Lmart89/MikroPrintr-3D/3D RENDERS/MK2560EM-G v1G-6.png

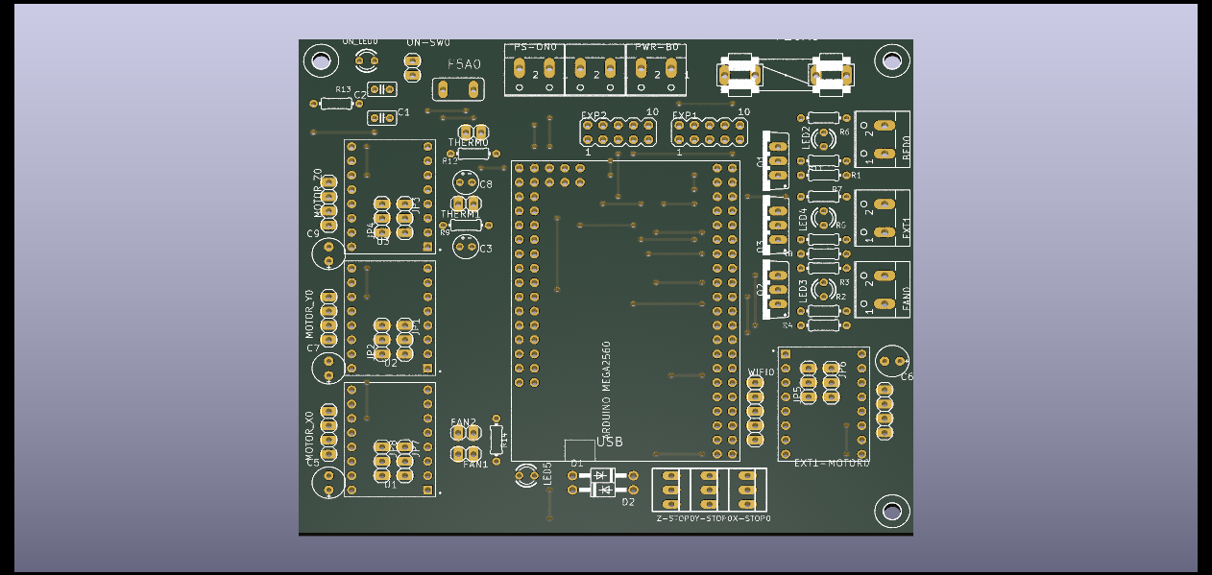
3D RENDERS/MK2560EM-G v1G-6.png
