Lmart89/MikroPrintr-3D/3D RENDERS/MK2560EM-G v1G-FLAT_PCB_SIZES.png

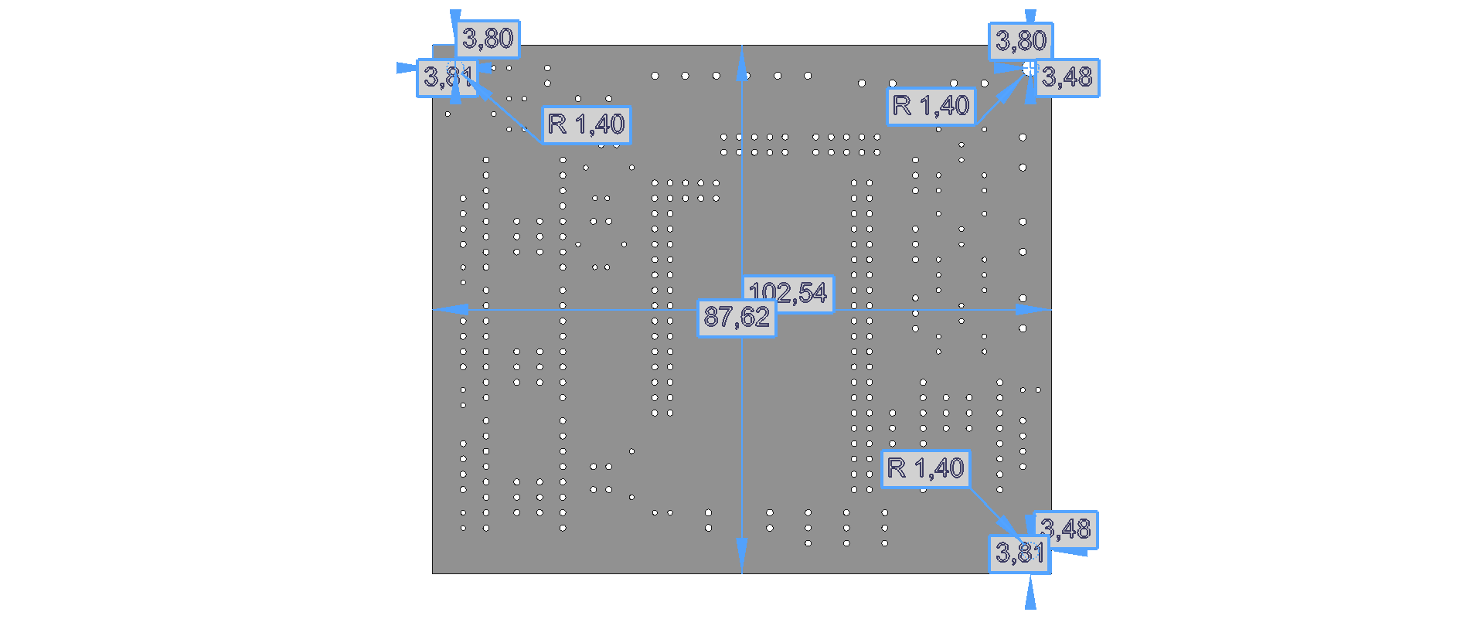
3D RENDERS/MK2560EM-G v1G-FLAT_PCB_SIZES.png
