Lmart89/MikroPrintr-3D/DIAGRAMAS/MK2560EMG-V2/mk2560G-v2.png

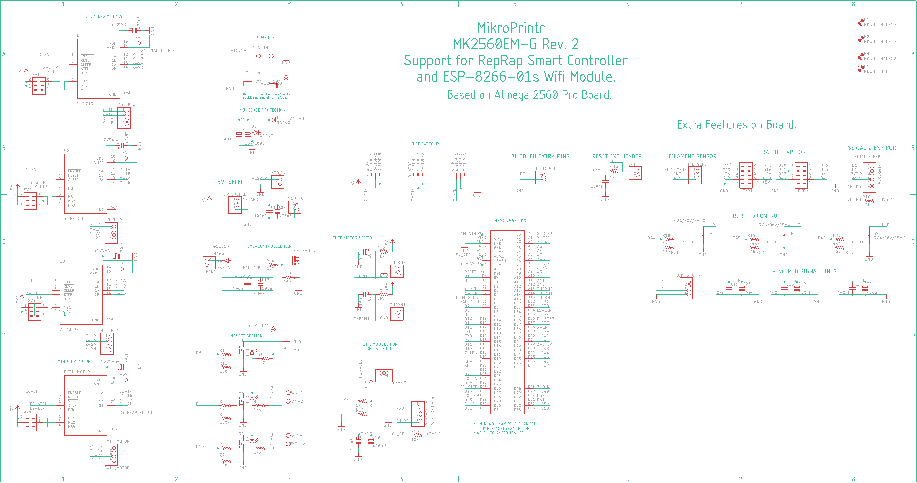
DIAGRAMAS/MK2560EMG-V2/mk2560G-v2.png
