Lmart89/MikroPrintr-3D/Printable Parts/Skylab Variant/medidas_skylab/Extrusor_12 dimensiones 3.png

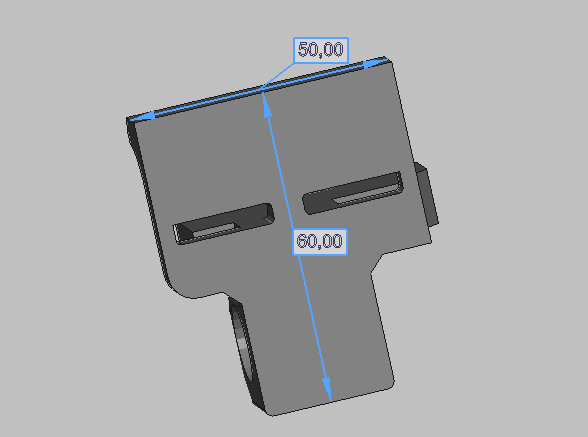
Printable Parts/Skylab Variant/medidas_skylab/Extrusor_12 dimensiones 3.png
