Lmart89/MikroPrintr-3D/Printable Parts/Skylab Variant/medidas_skylab/Z1 dimensiones 2.png

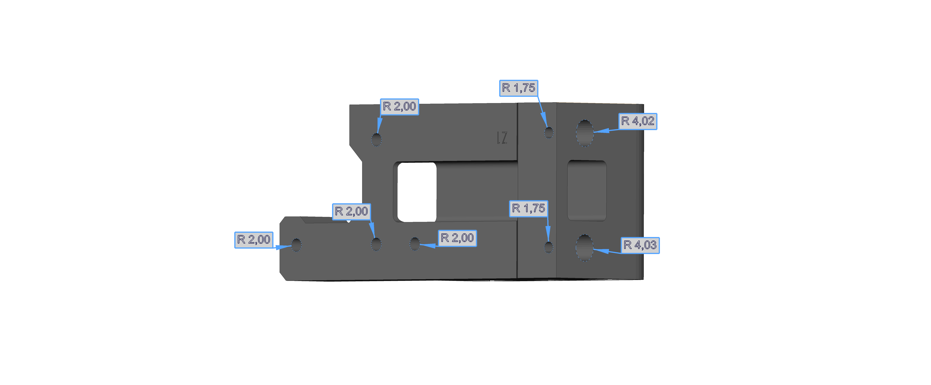
Printable Parts/Skylab Variant/medidas_skylab/Z1 dimensiones 2.png
