Lmart89/MikroPrintr-3D/Printable Parts/ME_Mini_3D_Printer/files/Blue_-_Idler_Holder.stl

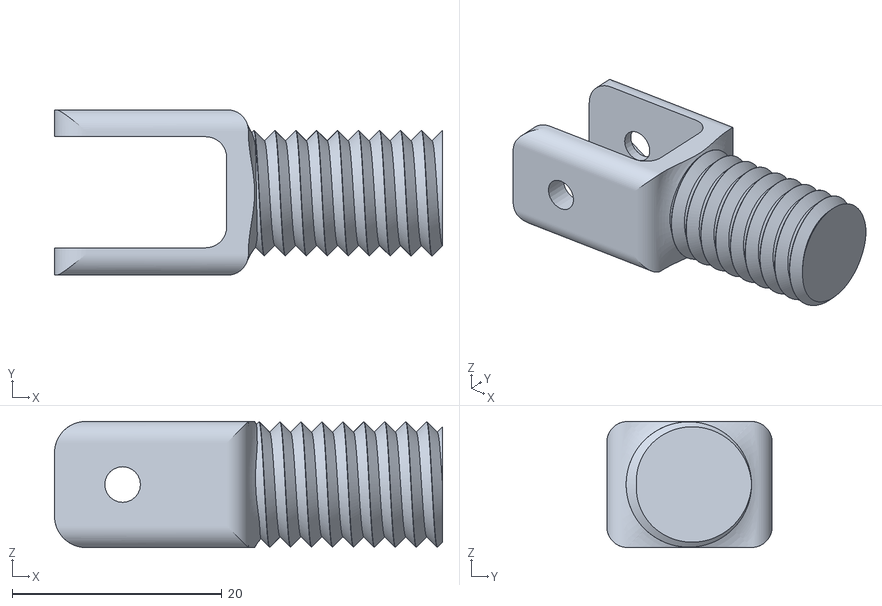
[picture p37: CAD file, 2023-07-11]
Printable Parts/ME_Mini_3D_Printer/files/Blue_-_Idler_Holder.stl
37.0 x 15.8 x 12.0
