Lmart89/MikroPrintr-3D/Printable Parts/MK-Parts V2/mk-cable-clip.stl

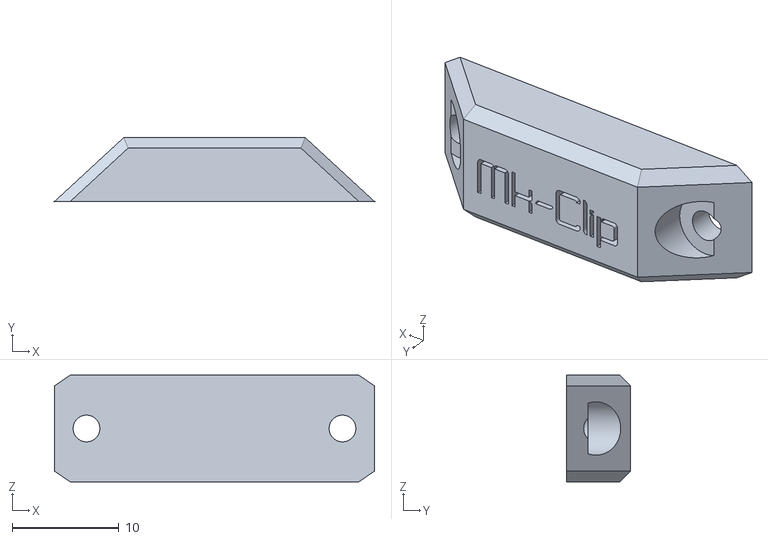
[picture p38: CAD file, 2025-04-13]
Printable Parts/MK-Parts V2/mk-cable-clip.stl
30.0 x 6.00 x 10.0
