Lmart89/MikroPrintr-3D/Printable Parts/ME_Mini_3D_Printer/files/Black_-_Back_Base_Plate.stl

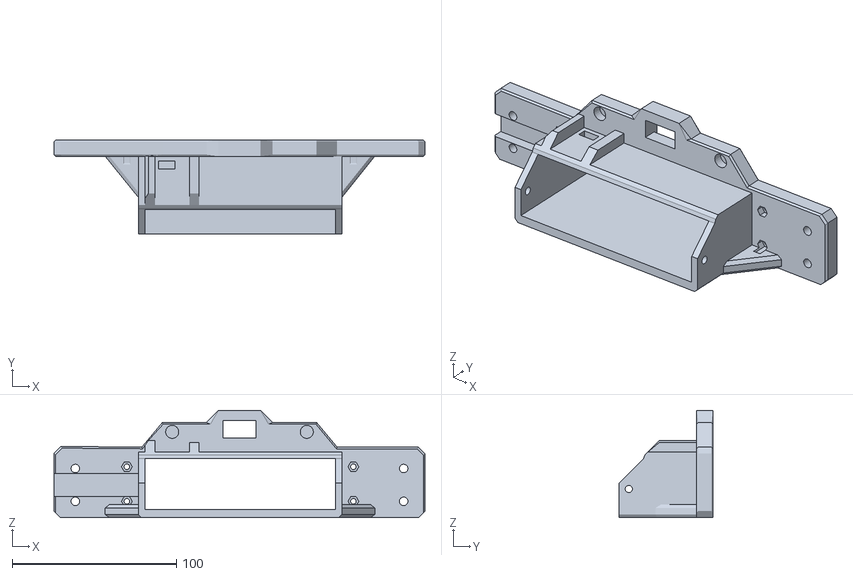
[picture p39: CAD file, 2023-07-11]
Printable Parts/ME_Mini_3D_Printer/files/Black_-_Back_Base_Plate.stl
226.0 x 57.4 x 65.4
