Lmart89/MikroPrintr-3D/Printable Parts/ME_Mini_3D_Printer/files/Blue_-_Hotend_Holder.stl

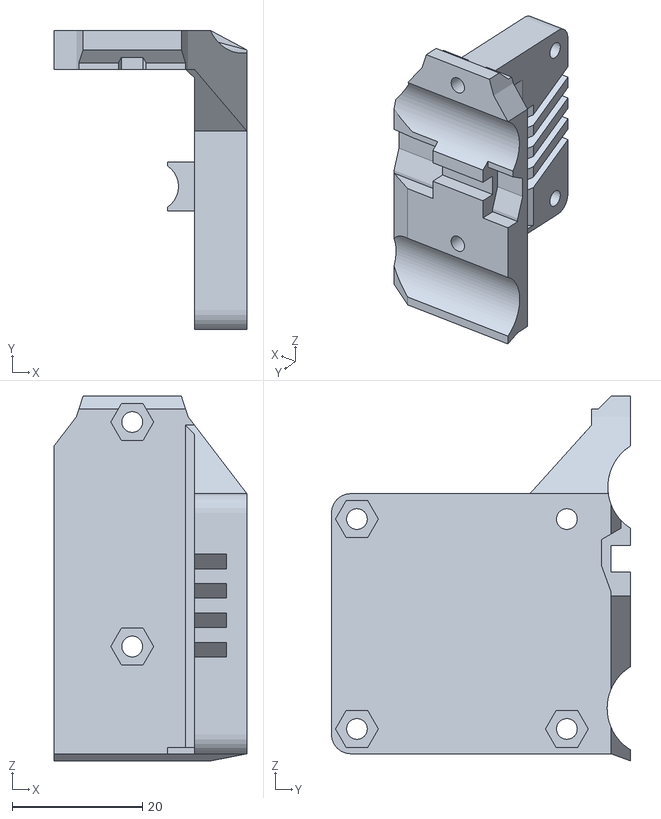
[picture p41: CAD file, 2023-07-11]
Printable Parts/ME_Mini_3D_Printer/files/Blue_-_Hotend_Holder.stl
29.6 x 46.0 x 56.1
