Lmart89/MikroPrintr-3D/Printable Parts/MK-Parts V2/mk_psu_cover.stl

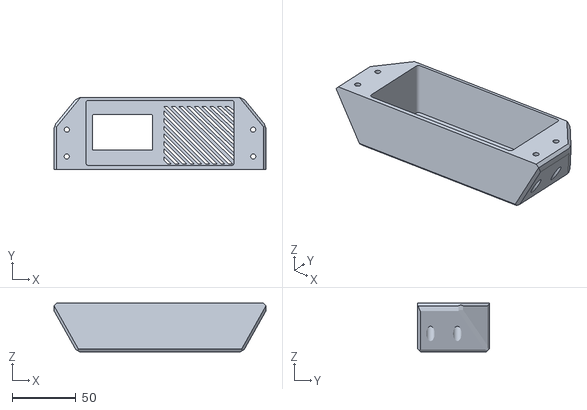
[picture p42: CAD file, 2025-04-05]
Printable Parts/MK-Parts V2/mk_psu_cover.stl
166.0 x 56.0 x 38.0
