Lmart89/MikroPrintr-3D/Printable Parts/ME_Mini_3D_Printer/files/Blue_-_Extruder_Idler.stl

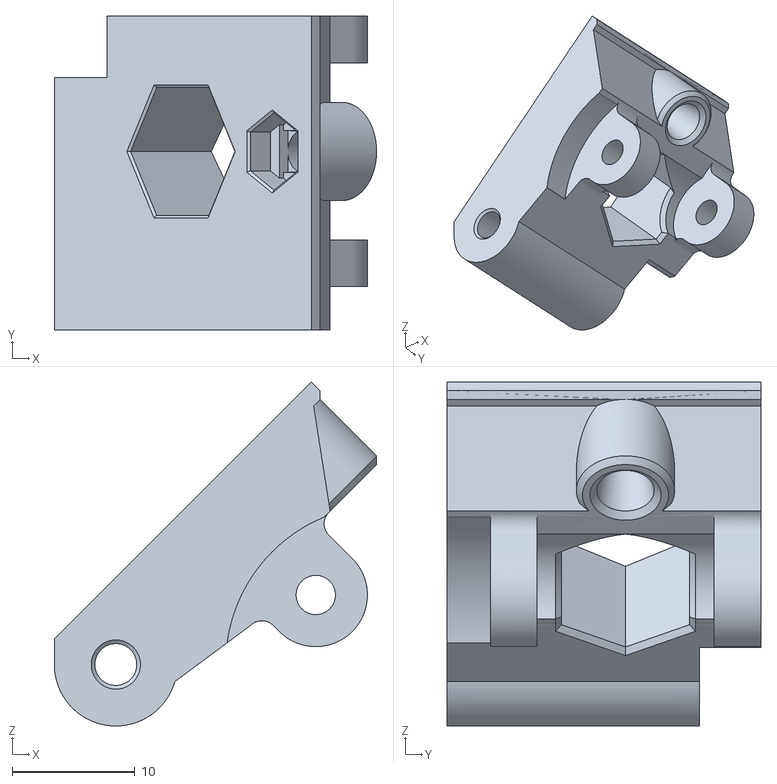
[picture p43: CAD file, 2023-07-11]
Printable Parts/ME_Mini_3D_Printer/files/Blue_-_Extruder_Idler.stl
26.2 x 25.5 x 28.0
