Lmart89/MikroPrintr-3D/Printable Parts/MK-Parts V2/mk_back_base_v2.stl

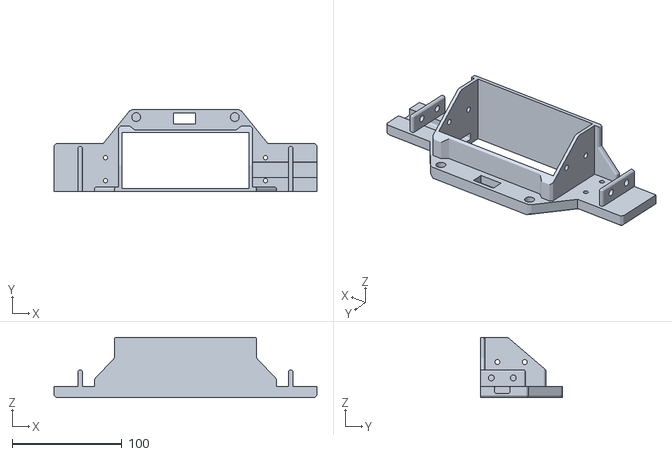
[picture p44: CAD file, 2025-04-05]
Printable Parts/MK-Parts V2/mk_back_base_v2.stl
240.0 x 75.0 x 55.0
