Lmart89/MikroPrintr-3D/Printable Parts/ME_Mini_3D_Printer/files/Blue_-_Hotend_Fan_Holder.stl

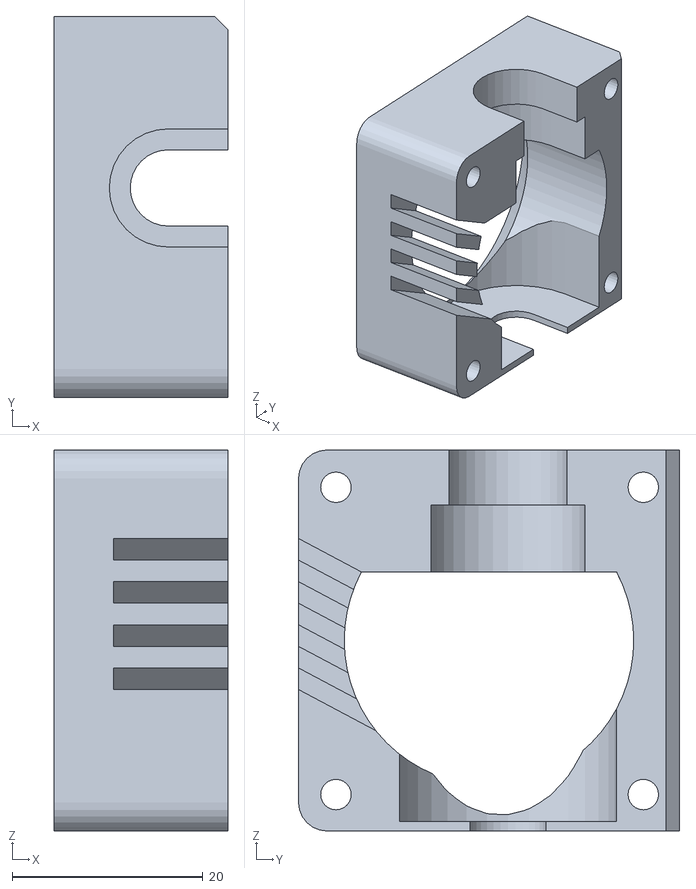
[picture p45: CAD file, 2023-07-11]
Printable Parts/ME_Mini_3D_Printer/files/Blue_-_Hotend_Fan_Holder.stl
18.3 x 40.0 x 40.0
