Lmart89/MikroPrintr-3D/Printable Parts/ME_Mini_3D_Printer/files/Black_-_Z_Probe_Suporte.stl

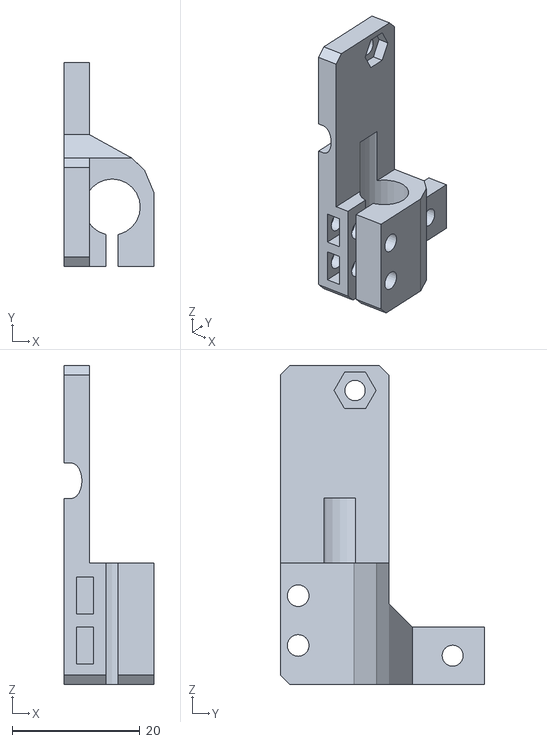
[picture p46: CAD file, 2023-07-11]
Printable Parts/ME_Mini_3D_Printer/files/Black_-_Z_Probe_Suporte.stl
14.2 x 32.0 x 50.0
