Lmart89/MikroPrintr-3D/Printable Parts/ME_Mini_3D_Printer/files/Blue_-_MKS_Display_Housing.stl

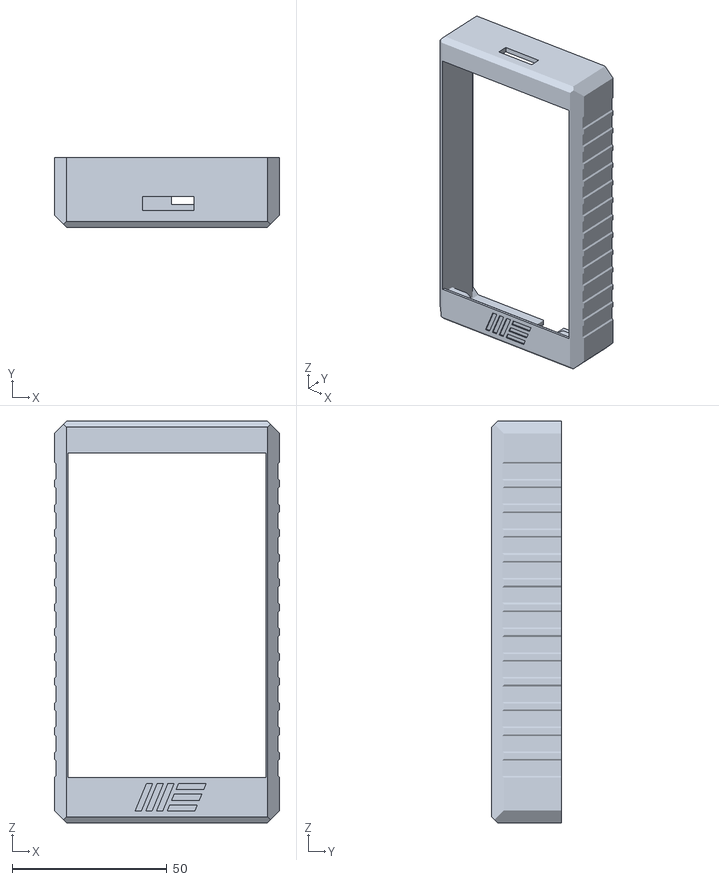
[picture p47: CAD file, 2023-07-11]
Printable Parts/ME_Mini_3D_Printer/files/Blue_-_MKS_Display_Housing.stl
72.9 x 22.6 x 129.9
