Lmart89/MikroPrintr-3D/Printable Parts/ME_Mini_3D_Printer/files/Black_-_Makerbase_Housing_Cover.stl

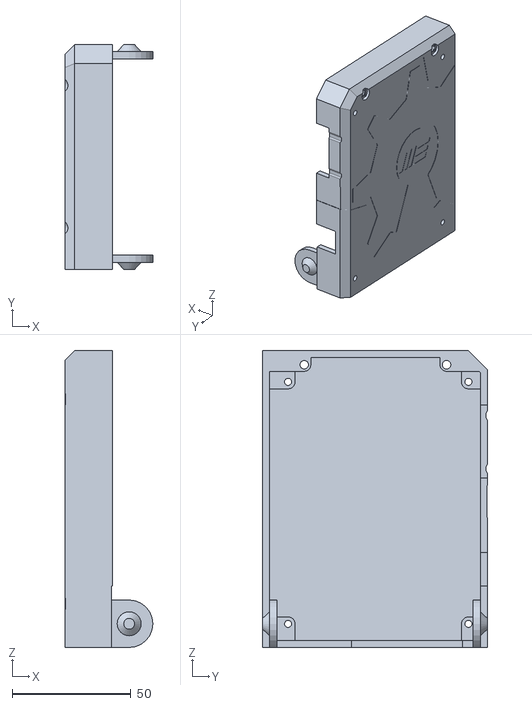
[picture p48: CAD file, 2023-07-11]
Printable Parts/ME_Mini_3D_Printer/files/Black_-_Makerbase_Housing_Cover.stl
37.0 x 94.8 x 125.2
