Lmart89/MikroPrintr-3D/Printable Parts/ME_Mini_3D_Printer/files/Black_-_FS_Leaver.stl

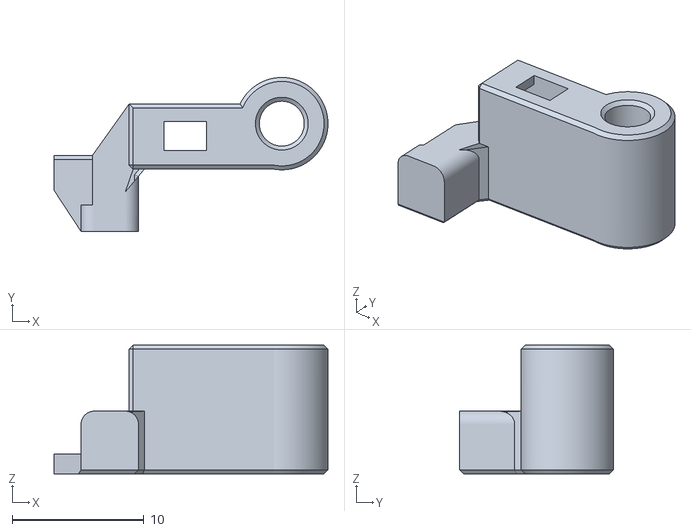
[picture p49: CAD file, 2023-07-11]
Printable Parts/ME_Mini_3D_Printer/files/Black_-_FS_Leaver.stl
20.8 x 11.7 x 9.75
