Lmart89/MikroPrintr-3D/Printable Parts/ME_Mini_3D_Printer/files/Blue_-_Extruder_Nozzel_Carriage.stl

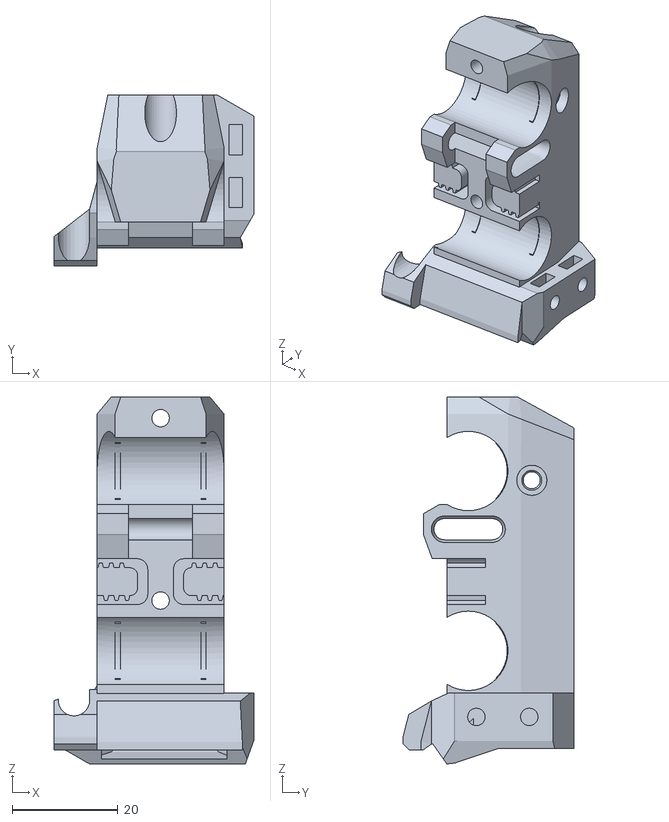
[picture p50: CAD file, 2023-07-11]
Printable Parts/ME_Mini_3D_Printer/files/Blue_-_Extruder_Nozzel_Carriage.stl
37.7 x 32.4 x 69.4
