Lmart89/MikroPrintr-3D/Printable Parts/ME_Mini_3D_Printer/files/Blue_-_Z_Motor_Mount.stl

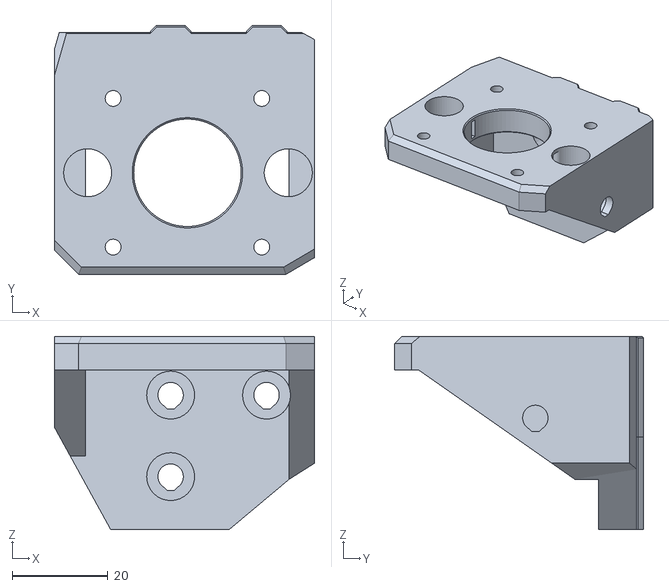
[picture p51: CAD file, 2023-07-11]
Printable Parts/ME_Mini_3D_Printer/files/Blue_-_Z_Motor_Mount.stl
54.2 x 51.9 x 40.3
