Lmart89/MikroPrintr-3D/Printable Parts/ME_Mini_3D_Printer/files/Blue_-_Y_Belt_Holder.stl

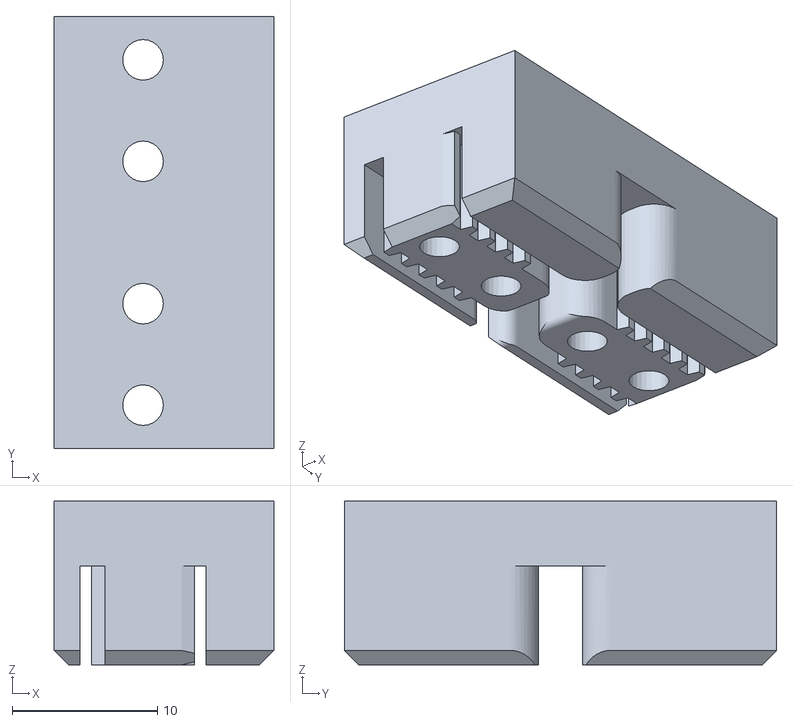
[picture p52: CAD file, 2023-07-11]
Printable Parts/ME_Mini_3D_Printer/files/Blue_-_Y_Belt_Holder.stl
15.2 x 29.8 x 11.3
