Lmart89/MikroPrintr-3D/Printable Parts/ME_Mini_3D_Printer/files/Black_-_Makerbase_Board_Housing.stl

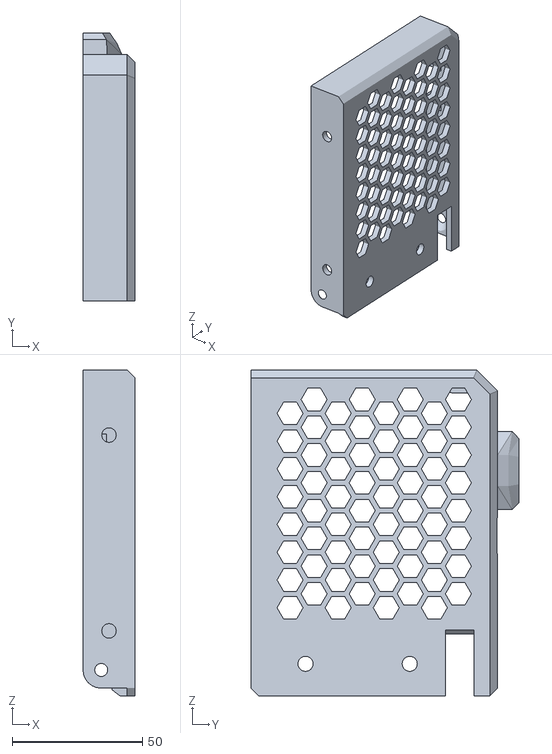
[picture p53: CAD file, 2023-07-11]
Printable Parts/ME_Mini_3D_Printer/files/Black_-_Makerbase_Board_Housing.stl
20.0 x 103.0 x 125.2
