Lmart89/MikroPrintr-3D/Printable Parts/ME_Mini_3D_Printer/files/Black_-_MKS_Adaptor_Cover.stl

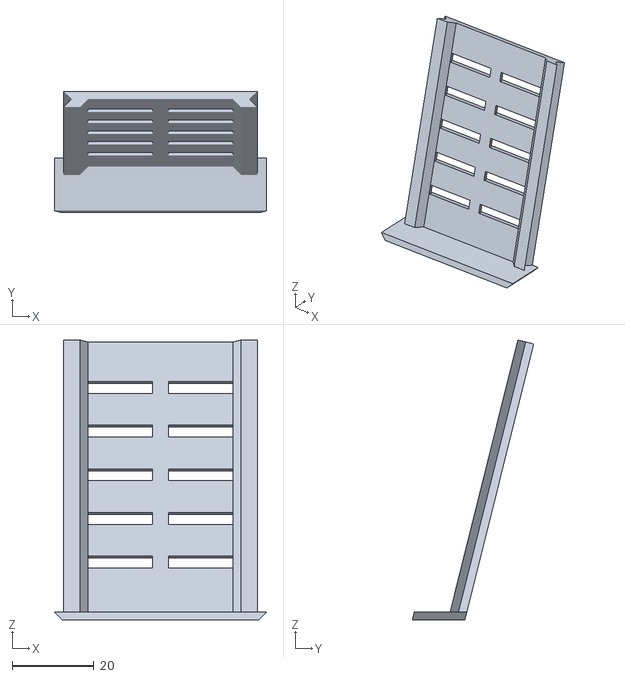
[picture p54: CAD file, 2023-07-11]
Printable Parts/ME_Mini_3D_Printer/files/Black_-_MKS_Adaptor_Cover.stl
52.0 x 29.7 x 68.5
