Lmart89/MikroPrintr-3D/Printable Parts/ME_Mini_3D_Printer/files/Black_-_Front_Base_Plate.stl

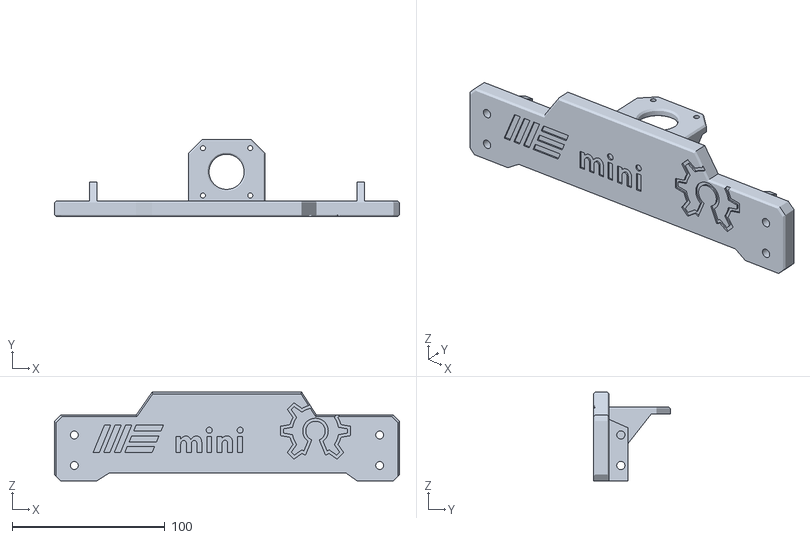
[picture p55: CAD file, 2023-07-11]
Printable Parts/ME_Mini_3D_Printer/files/Black_-_Front_Base_Plate.stl
226.0 x 50.2 x 58.0
