Lmart89/MikroPrintr-3D/Printable Parts/ME_Mini_3D_Printer/files/Blue_-_Bed_Wire_Cover_A.stl

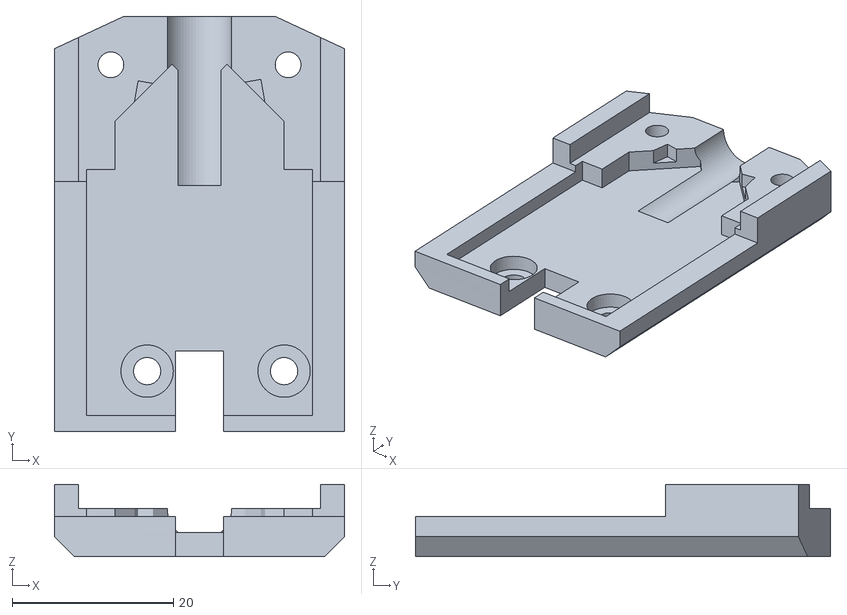
[picture p56: CAD file, 2023-07-11]
Printable Parts/ME_Mini_3D_Printer/files/Blue_-_Bed_Wire_Cover_A.stl
36.0 x 51.5 x 9.00
