Lmart89/MikroPrintr-3D/Printable Parts/ME_Mini_3D_Printer/files/Blue_-_X_Idler.stl

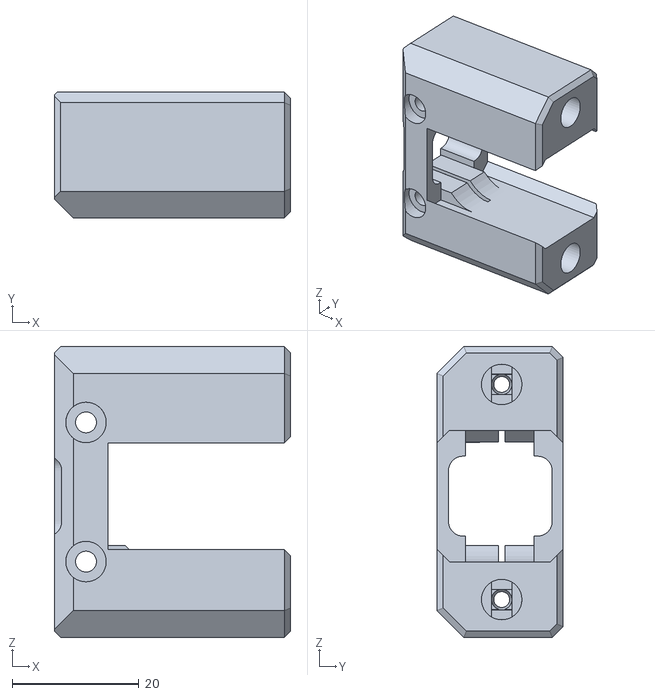
[picture p57: CAD file, 2023-07-11]
Printable Parts/ME_Mini_3D_Printer/files/Blue_-_X_Idler.stl
37.3 x 20.0 x 46.0
