Lmart89/MikroPrintr-3D/Printable Parts/ME_Mini_3D_Printer/files/Black_-_Z_End_Cap.stl

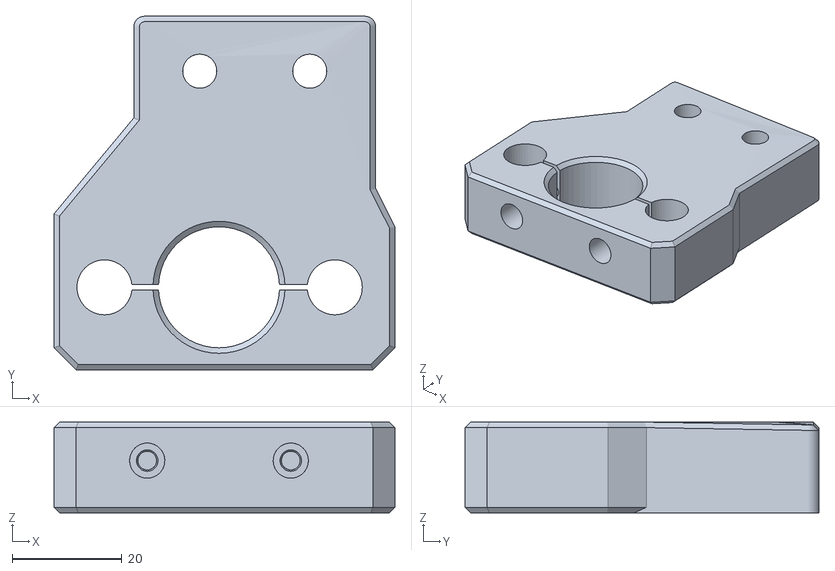
[picture p58: CAD file, 2023-07-11]
Printable Parts/ME_Mini_3D_Printer/files/Black_-_Z_End_Cap.stl
62.0 x 64.3 x 16.5
