Lmart89/MikroPrintr-3D/Printable Parts/ME_Mini_3D_Printer/files/Blue_-_Tensioner_Base.stl

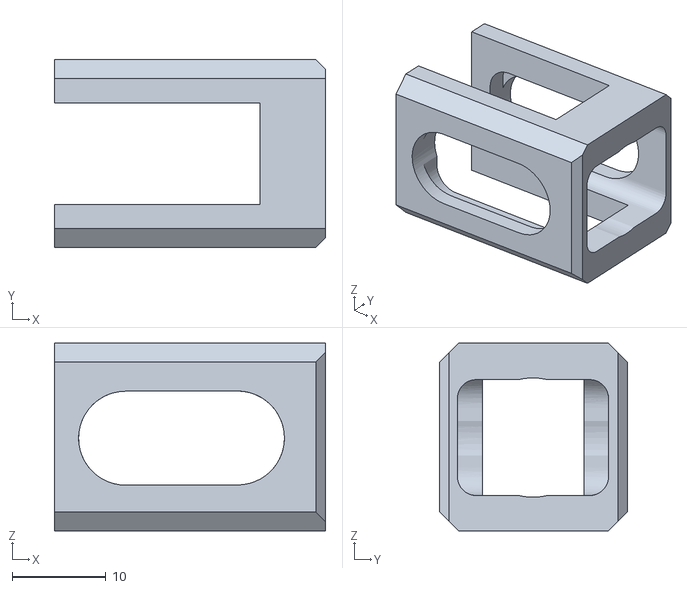
[picture p59: CAD file, 2023-07-11]
Printable Parts/ME_Mini_3D_Printer/files/Blue_-_Tensioner_Base.stl
28.8 x 20.0 x 20.0
