Lmart89/MikroPrintr-3D/Printable Parts/ME_Mini_3D_Printer/files/Black_-_Y_Carriage.3mf

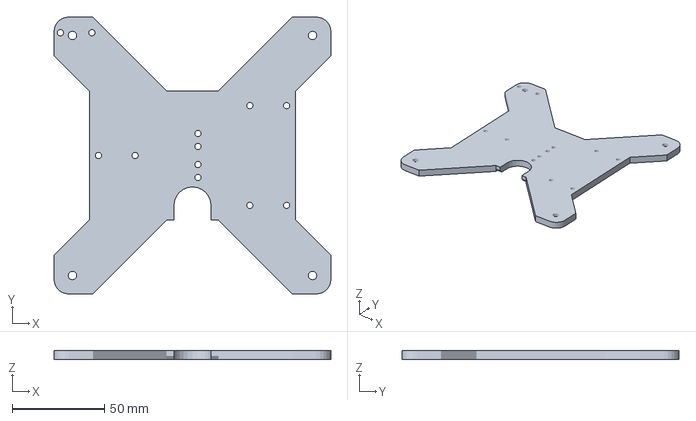
[picture p61: CAD file, 2023-07-11]
Printable Parts/ME_Mini_3D_Printer/files/Black_-_Y_Carriage.3mf
150.0 x 150.0 x 5.00 mm
