Lmart89/MikroPrintr-3D/Printable Parts/ME_Mini_3D_Printer/files/Blue_-_X_Motor_Carriage_Back.stl

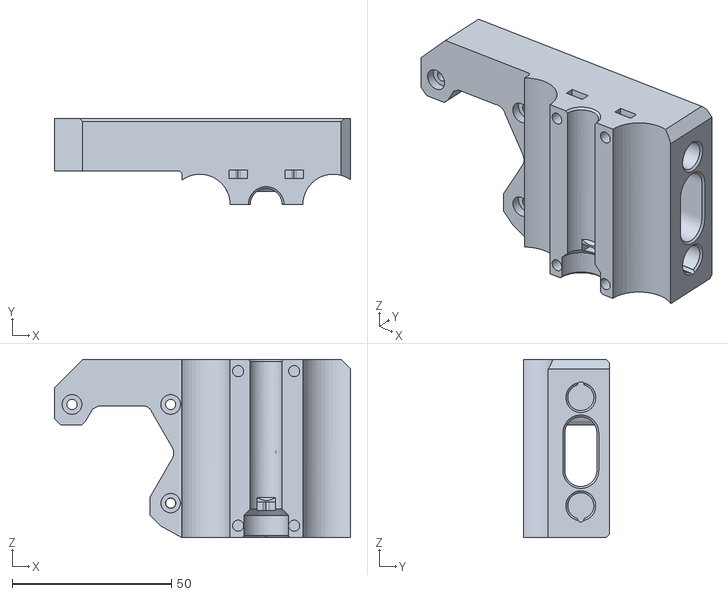
[picture p62: CAD file, 2023-07-11]
Printable Parts/ME_Mini_3D_Printer/files/Blue_-_X_Motor_Carriage_Back.stl
93.0 x 27.0 x 56.0
