Lmart89/MikroPrintr-3D/Printable Parts/ME_Mini_3D_Printer/files/Blue_-_Z_Endstop_Holder.stl

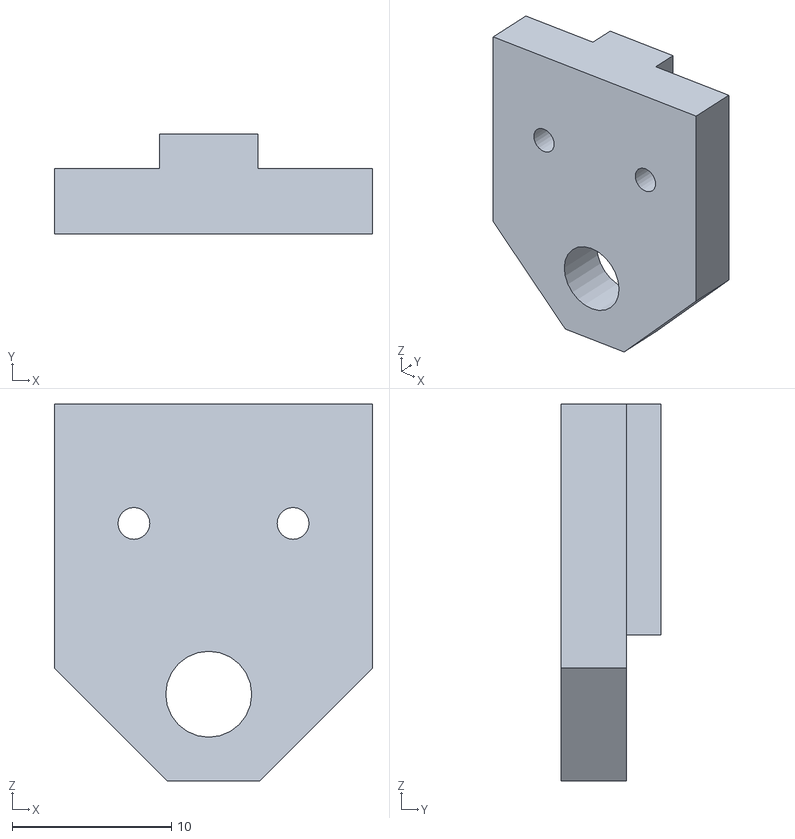
[picture p63: CAD file, 2023-07-11]
Printable Parts/ME_Mini_3D_Printer/files/Blue_-_Z_Endstop_Holder.stl
20.0 x 6.30 x 23.7
