Lmart89/MikroPrintr-3D/Printable Parts/ME_Mini_3D_Printer/files/Blue_-_Extruder_Support.stl

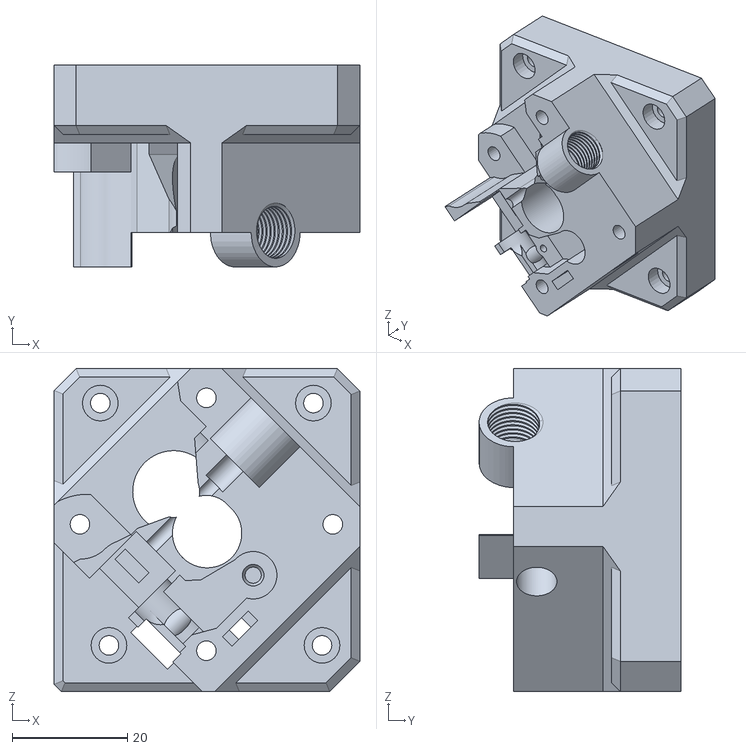
[picture p64: CAD file, 2023-07-11]
Printable Parts/ME_Mini_3D_Printer/files/Blue_-_Extruder_Support.stl
53.0 x 35.0 x 56.0
