Lmart89/MikroPrintr-3D/Printable Parts/ME_Mini_3D_Printer/files/Black_-_Bearing_Holder.stl

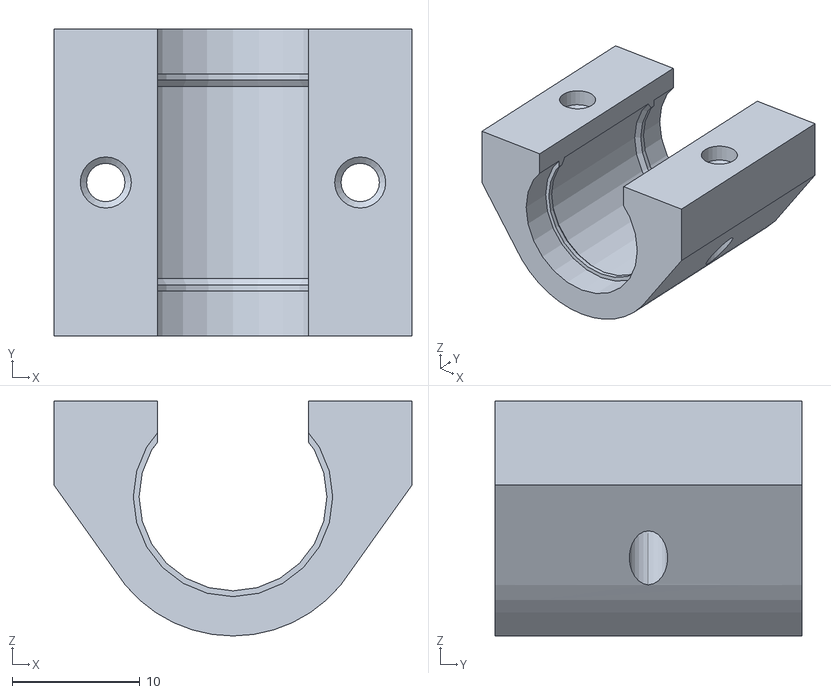
[picture p65: CAD file, 2023-07-11]
Printable Parts/ME_Mini_3D_Printer/files/Black_-_Bearing_Holder.stl
28.0 x 24.0 x 18.4
