Lmart89/MikroPrintr-3D/Printable Parts/ME_Mini_3D_Printer/files/Black_-_PSU_Cover.stl

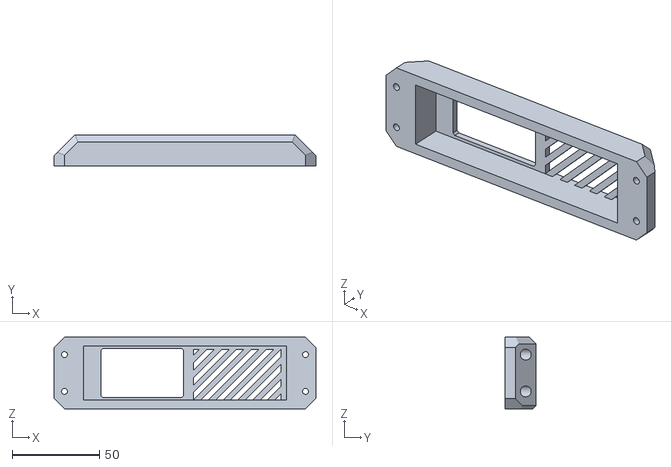
[picture p66: CAD file, 2023-07-11]
Printable Parts/ME_Mini_3D_Printer/files/Black_-_PSU_Cover.stl
150.0 x 18.0 x 41.0
