Lmart89/MikroPrintr-3D/Printable Parts/ME_Mini_3D_Printer/files/Black_-_Makerbase_Cable_Clip.stl

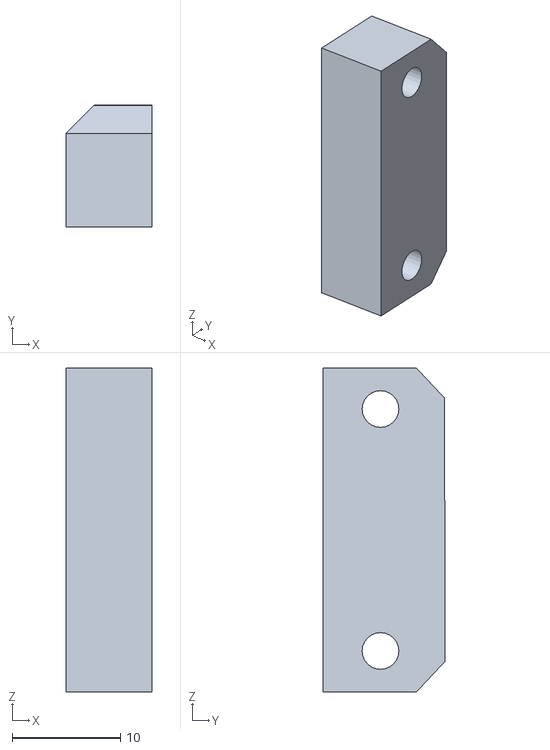
[picture p67: CAD file, 2023-07-11]
Printable Parts/ME_Mini_3D_Printer/files/Black_-_Makerbase_Cable_Clip.stl
8.00 x 11.3 x 30.0
