Lmart89/MikroPrintr-3D/Printable Parts/ME_Mini_3D_Printer/files/Black_-_FS_Adapter.stl

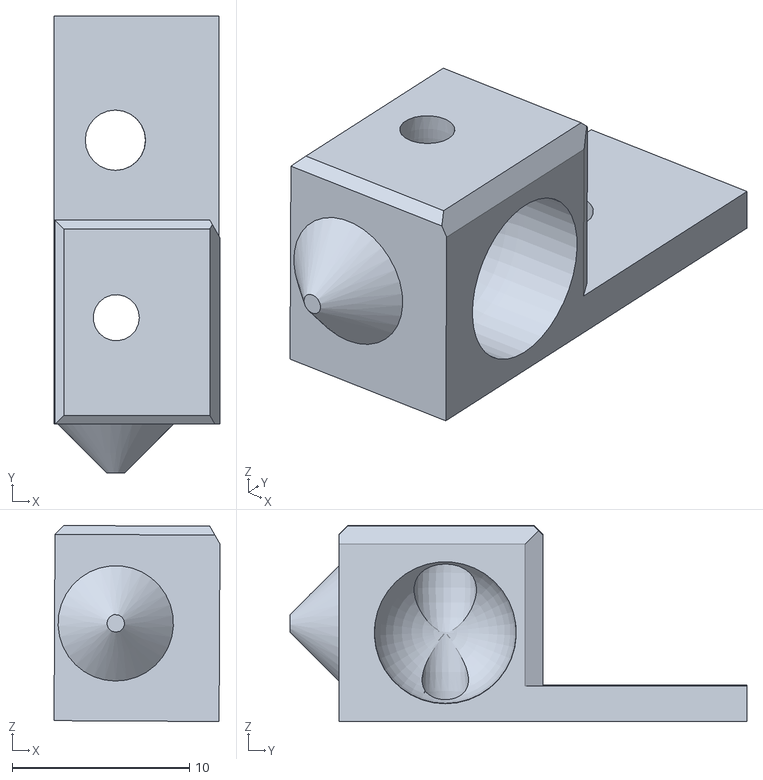
[picture p68: CAD file, 2023-07-11]
Printable Parts/ME_Mini_3D_Printer/files/Black_-_FS_Adapter.stl
9.35 x 25.8 x 11.0
