Lmart89/MikroPrintr-3D/Printable Parts/ME_Mini_3D_Printer/files/Blue_-_MKS_Display_Cover.stl

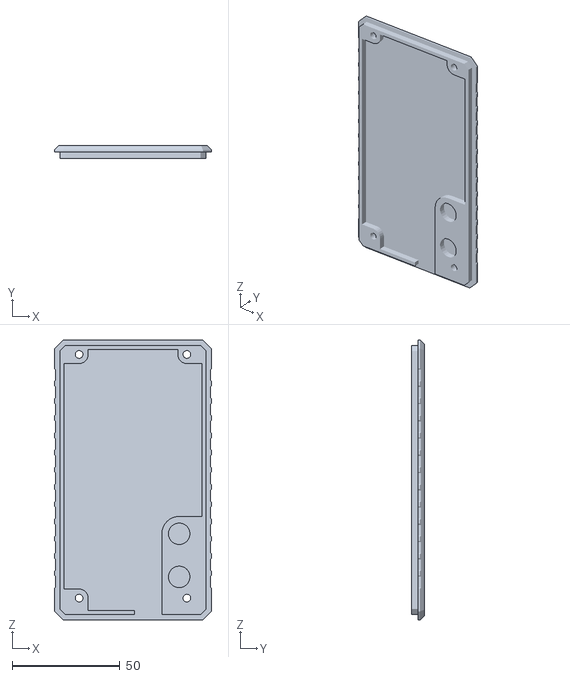
[picture p69: CAD file, 2023-07-11]
Printable Parts/ME_Mini_3D_Printer/files/Blue_-_MKS_Display_Cover.stl
72.9 x 6.00 x 129.9
