Lmart89/MikroPrintr-3D/Printable Parts/ME_Mini_3D_Printer/files/Black_-_Extruder_Strain_Relief.stl

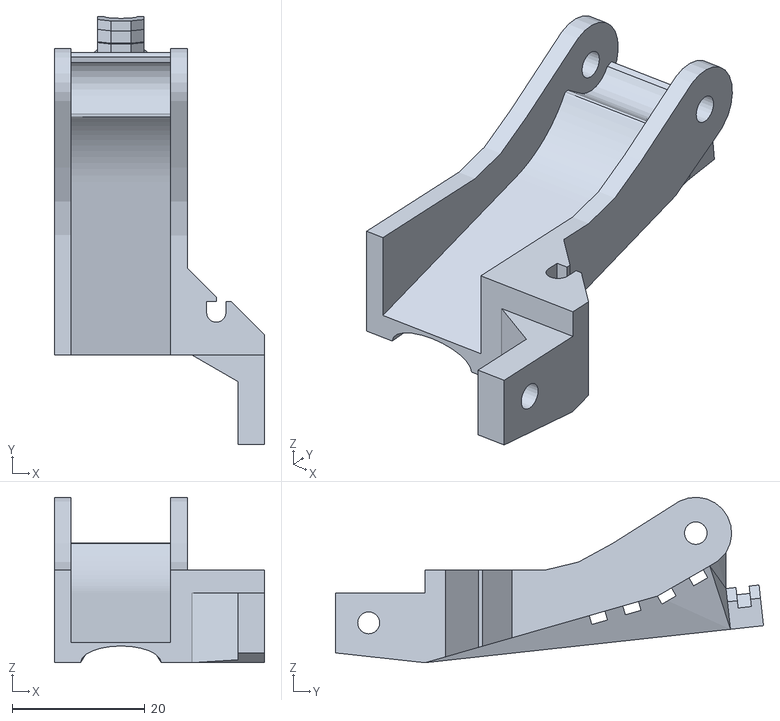
[picture p70: CAD file, 2023-07-11]
Printable Parts/ME_Mini_3D_Printer/files/Black_-_Extruder_Strain_Relief.stl
31.6 x 64.4 x 24.9
