Lmart89/MikroPrintr-3D/Printable Parts/ME_Mini_3D_Printer/images/ME_-_mini_-_12.jpg

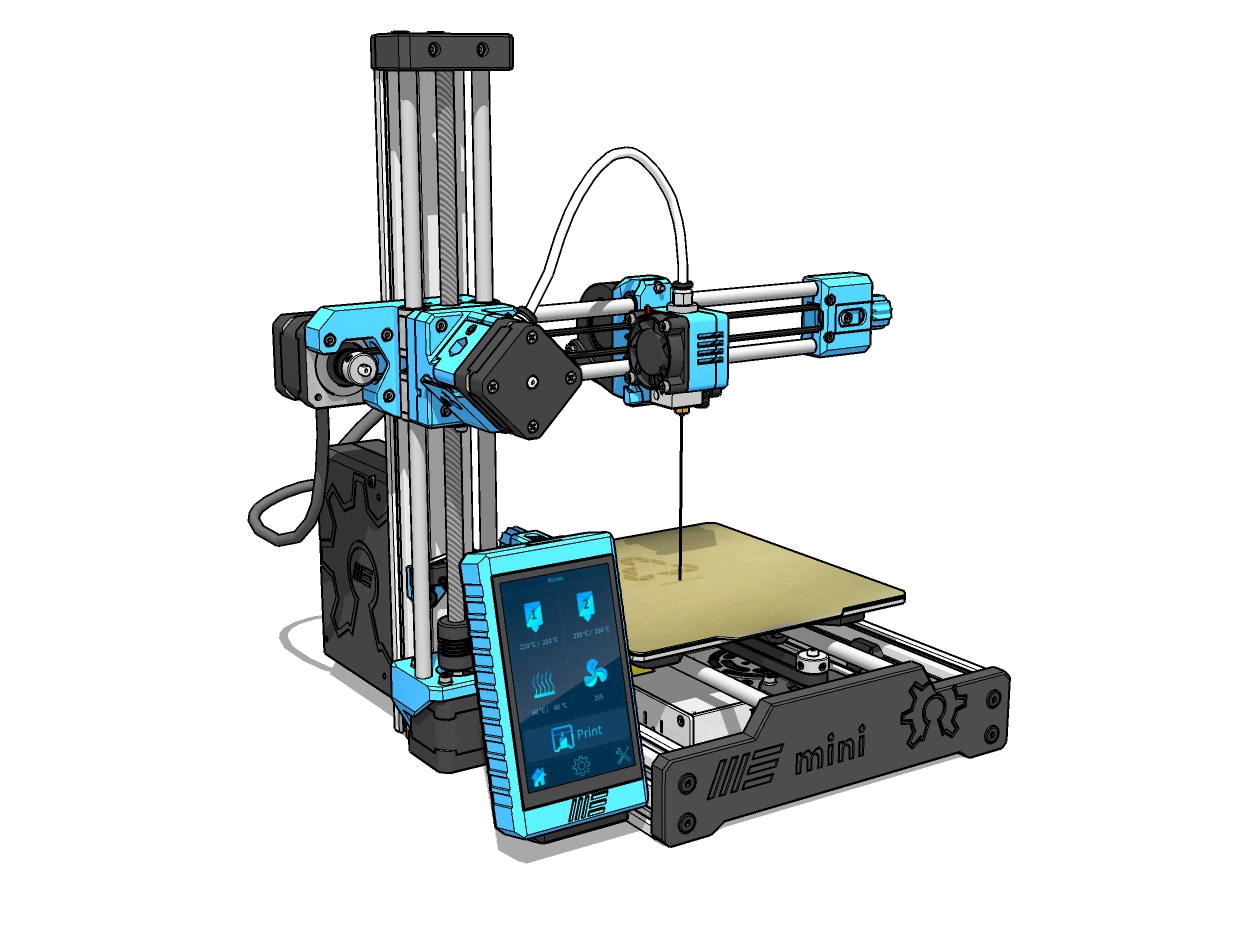
Printable Parts/ME_Mini_3D_Printer/images/ME_-_mini_-_12.jpg
